antmicro/signal-integrity-test-board/assets/previews/layer1.webp

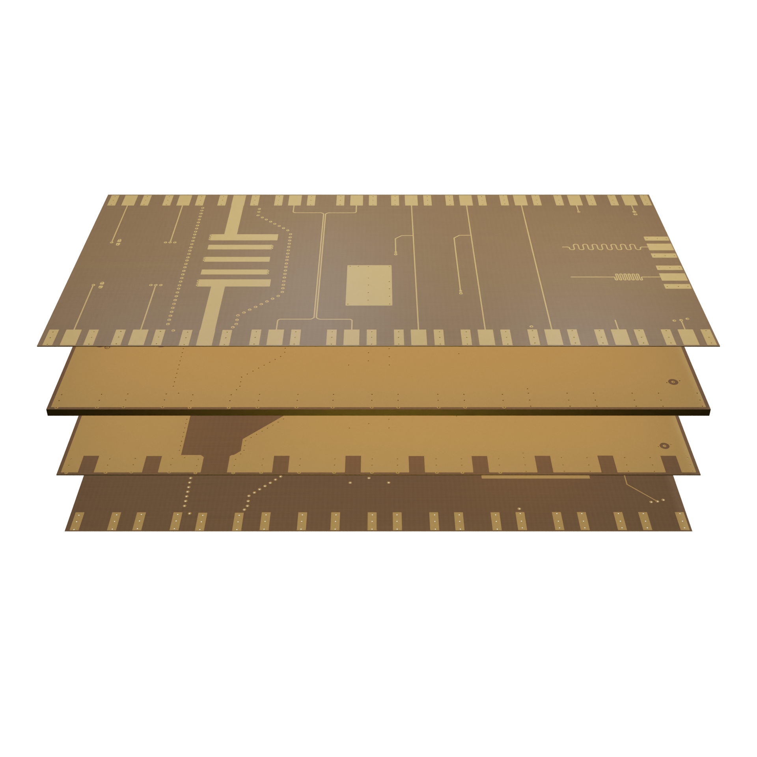
assets/previews/layer1.webp
