antmicro/signal-integrity-test-board/assets/previews/layer3.png

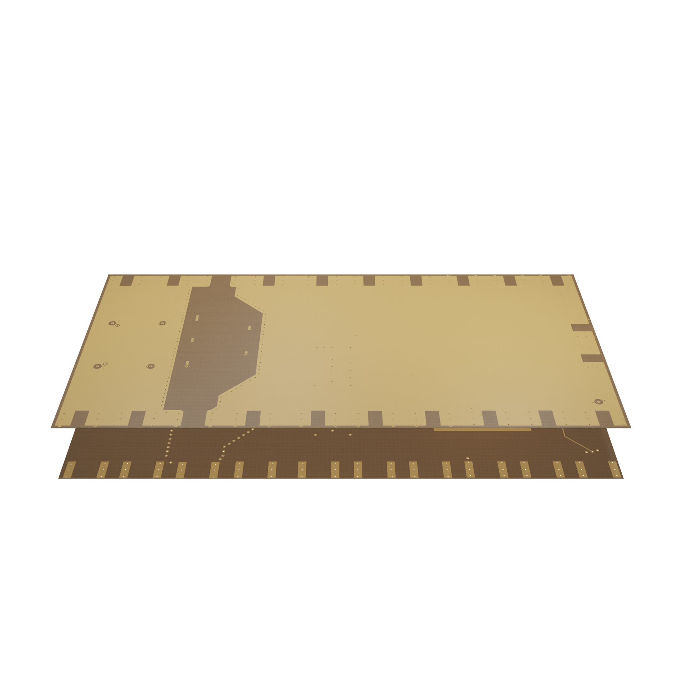
assets/previews/layer3.png
