antmicro/signal-integrity-test-board/assets/previews/layer4.png

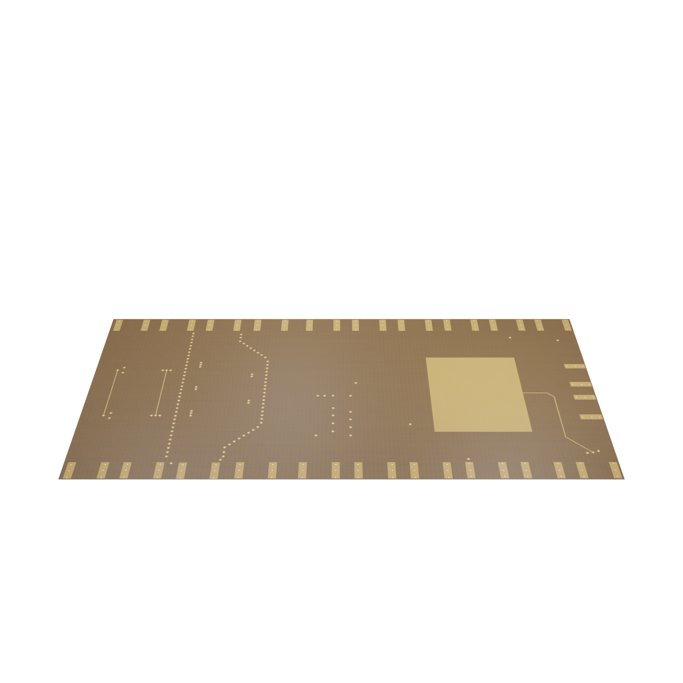
assets/previews/layer4.png
