antmicro/signal-integrity-test-board/assets/previews/leftB.png

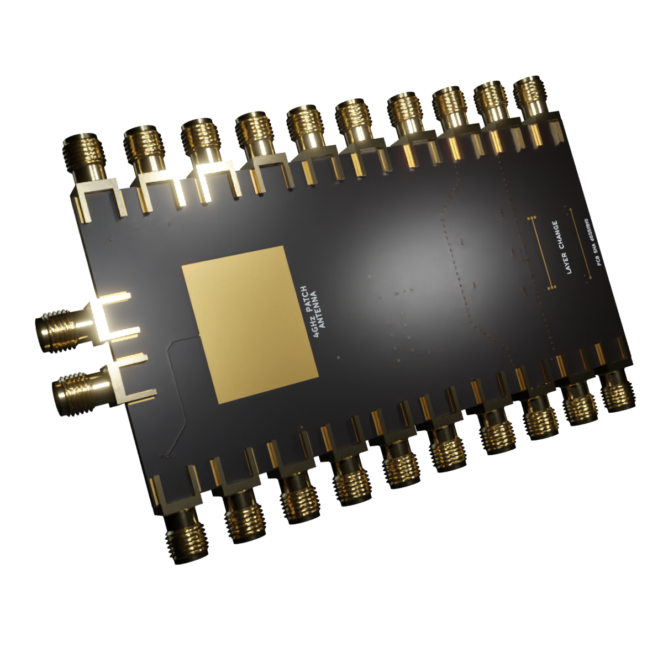
assets/previews/leftB.png
