antmicro/signal-integrity-test-board/assets/previews/leftT.png

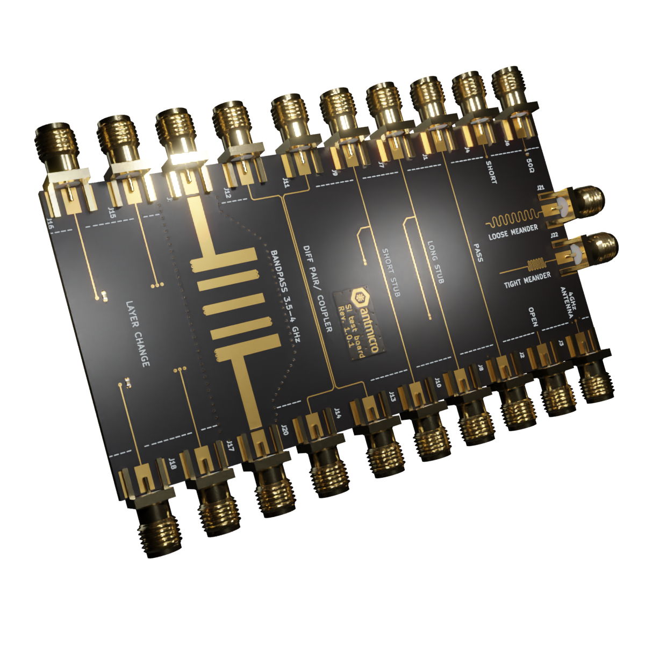
assets/previews/leftT.png
