antmicro/signal-integrity-test-board/assets/previews/orthoB.png

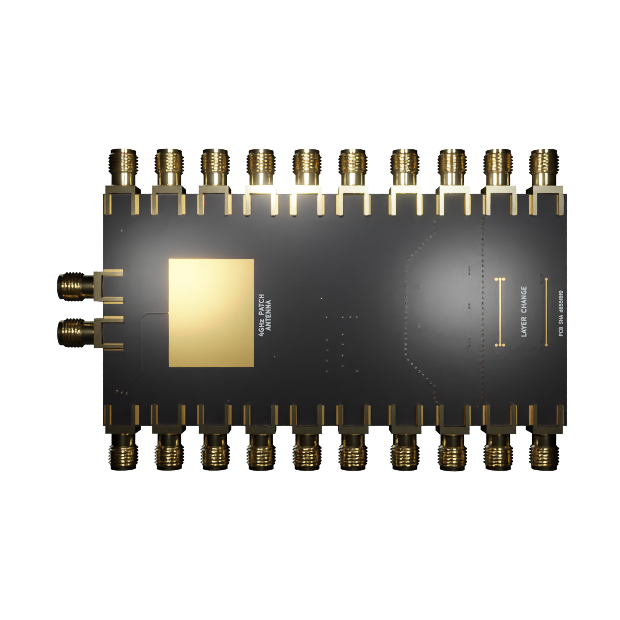
assets/previews/orthoB.png
