antmicro/signal-integrity-test-board/assets/previews/orthoT.png

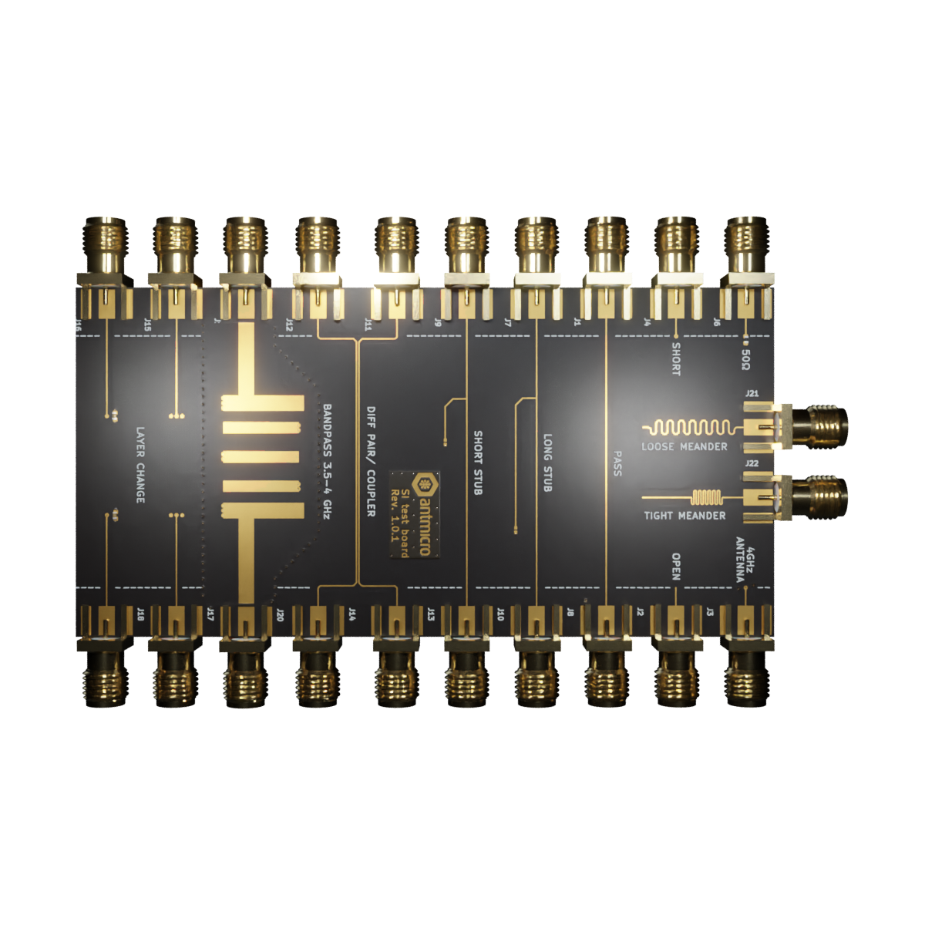
assets/previews/orthoT.png
