antmicro/signal-integrity-test-board/assets/previews/photoB.png

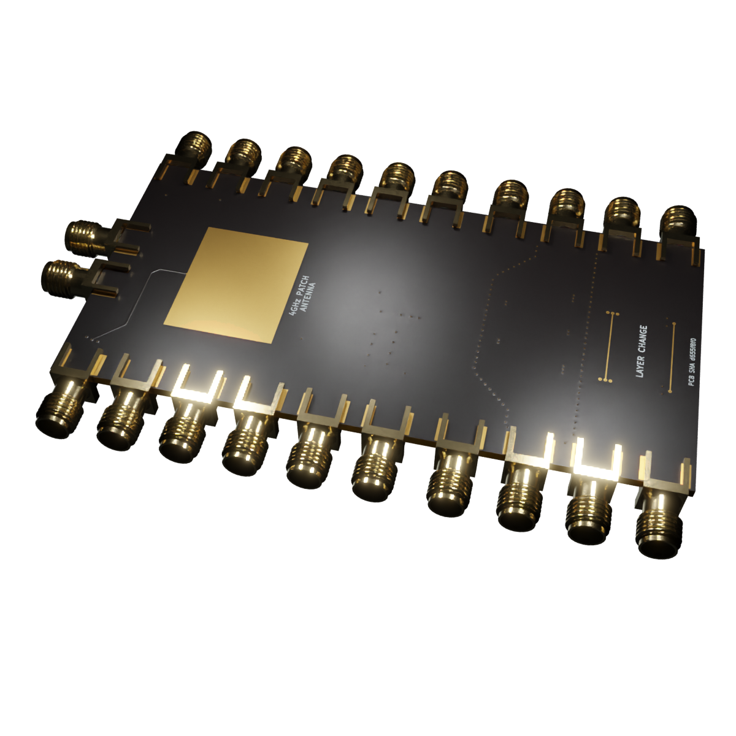
assets/previews/photoB.png
