antmicro/signal-integrity-test-board/assets/previews/photoT.png

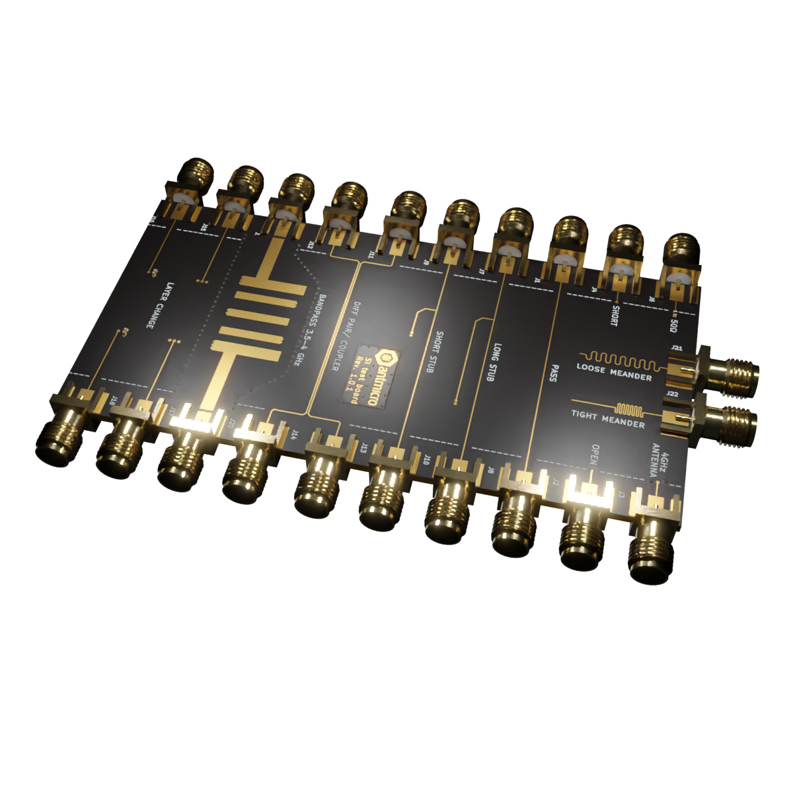
assets/previews/photoT.png
