antmicro/signal-integrity-test-board/assets/previews/rightB.png

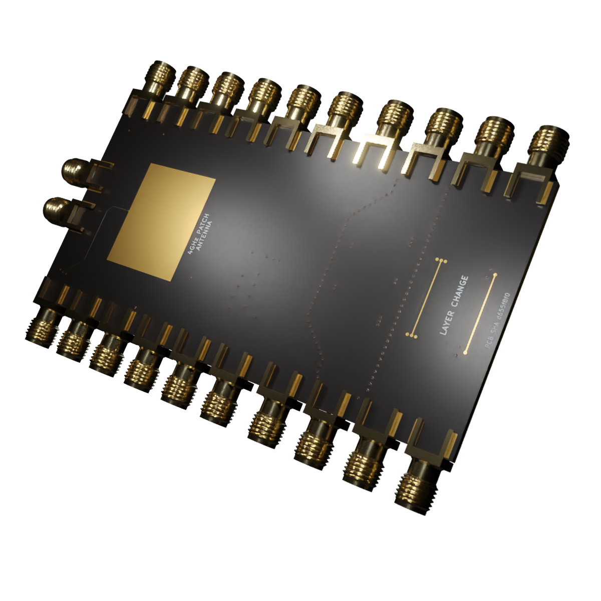
assets/previews/rightB.png
