antmicro/signal-integrity-test-board/assets/previews/rightT.png

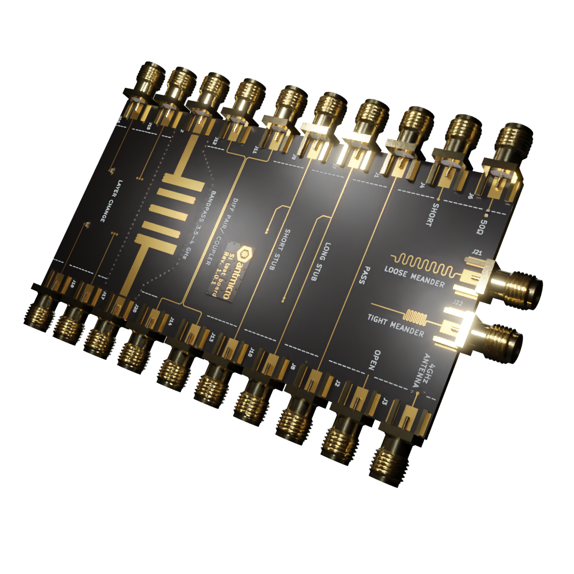
assets/previews/rightT.png
