antmicro/signal-integrity-test-board/assets/si/diff_pair/diff_delay.png

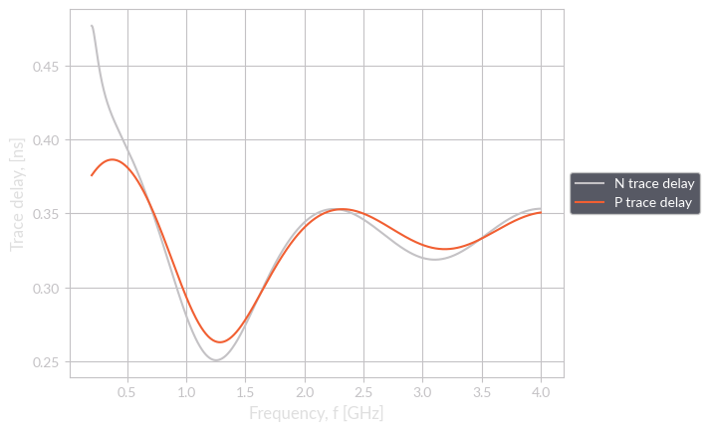
assets/si/diff_pair/diff_delay.png
