antmicro/signal-integrity-test-board/assets/si/diff_pair/S_11_smith.png

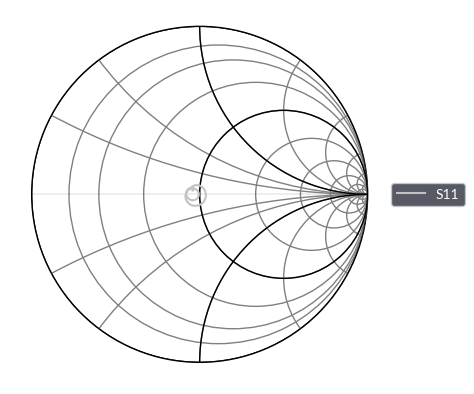
assets/si/diff_pair/S_11_smith.png
