antmicro/signal-integrity-test-board/assets/si/diff_pair/s_param_and_smith_1.png

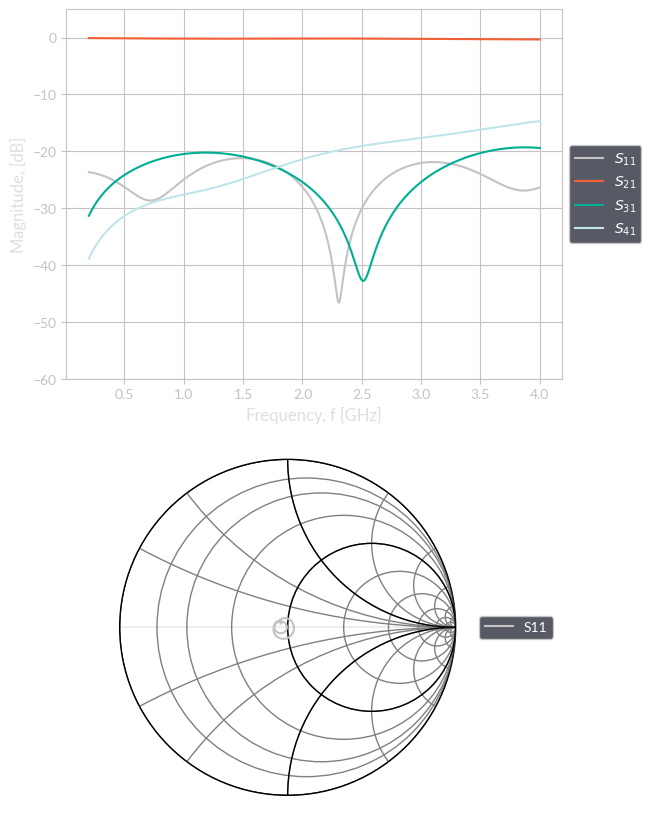
assets/si/diff_pair/s_param_and_smith_1.png
