antmicro/signal-integrity-test-board/assets/si/diff_pair/S_x3.png

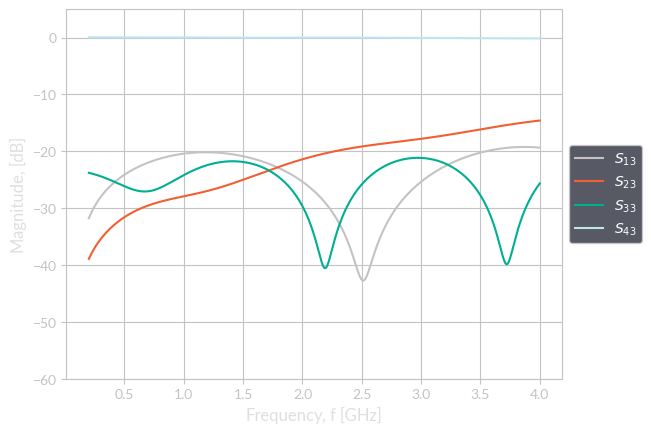
assets/si/diff_pair/S_x3.png
