antmicro/signal-integrity-test-board/assets/si/diff_pair/SDD_Diff.png

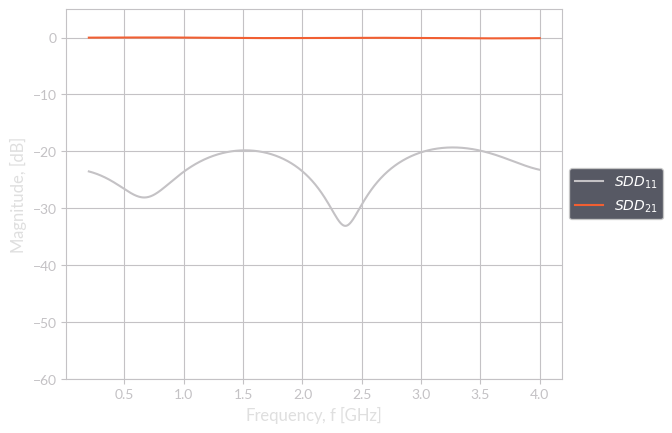
assets/si/diff_pair/SDD_Diff.png
