antmicro/signal-integrity-test-board/assets/si/diff_pair/top_view.png

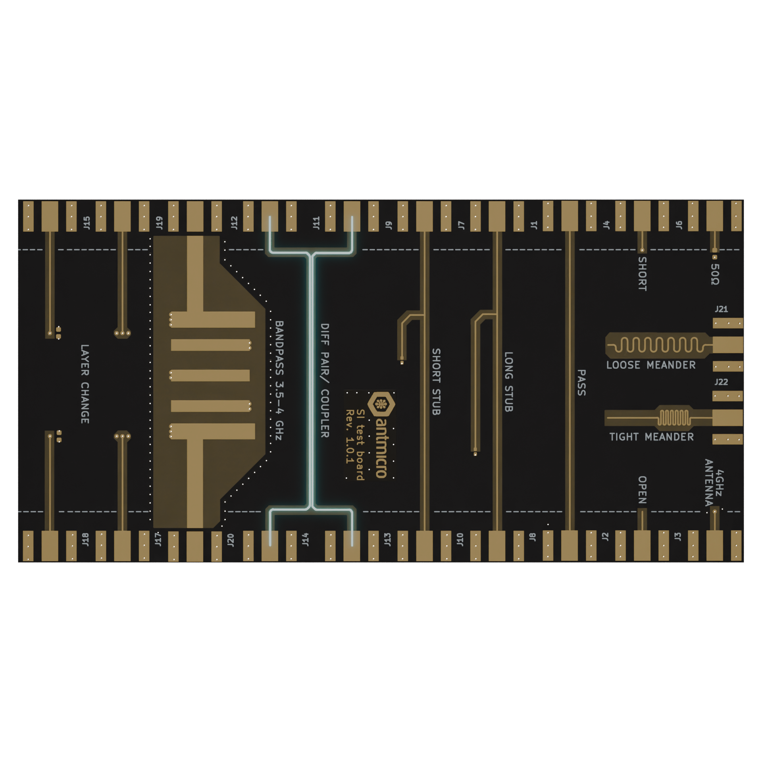
assets/si/diff_pair/top_view.png
