antmicro/signal-integrity-test-board/assets/si/diff_pair/Z_1.png

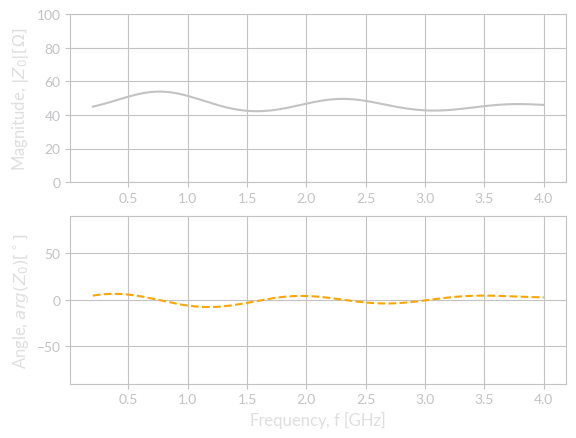
assets/si/diff_pair/Z_1.png
