antmicro/signal-integrity-test-board/assets/si/diff_pair/Z_diff.png

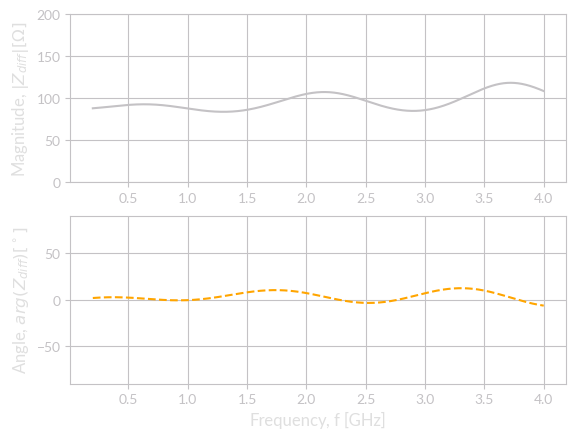
assets/si/diff_pair/Z_diff.png
