antmicro/signal-integrity-test-board/assets/si/layer-change-1/s_param_and_smith_1.png

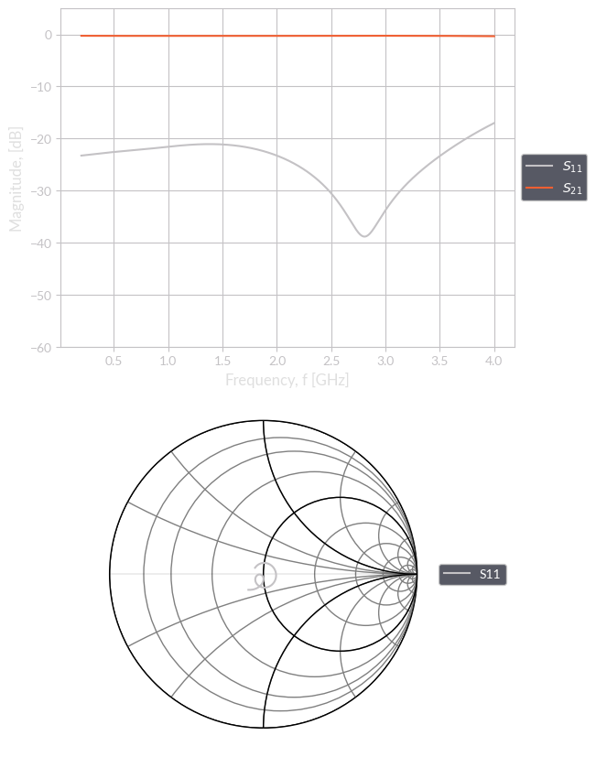
assets/si/layer-change-1/s_param_and_smith_1.png
