antmicro/signal-integrity-test-board/assets/si/layer-change-1/S_x1.png

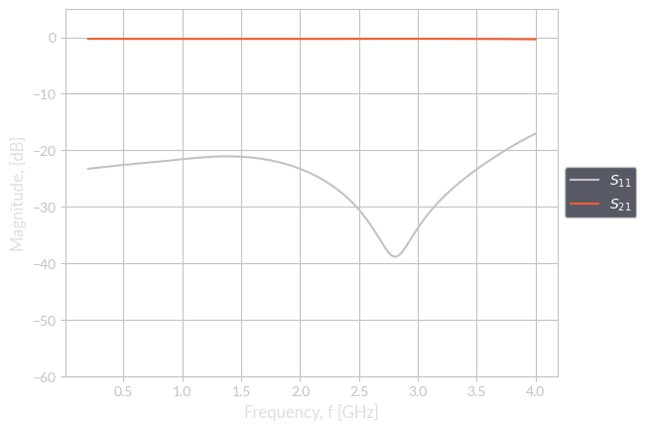
assets/si/layer-change-1/S_x1.png
