antmicro/signal-integrity-test-board/assets/si/layer-change-2/S_x1.png

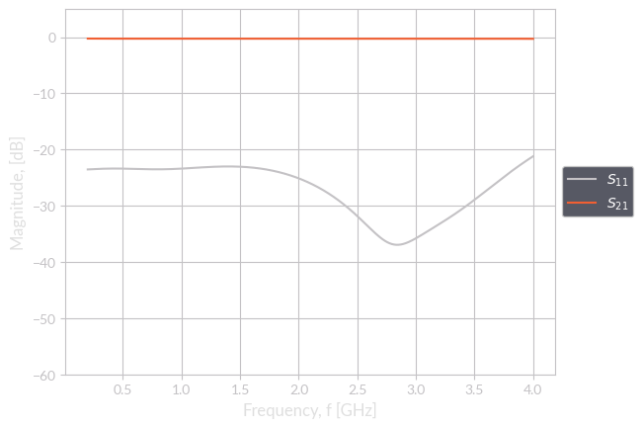
assets/si/layer-change-2/S_x1.png
