antmicro/signal-integrity-test-board/assets/si/long-stub/S_11_smith.png

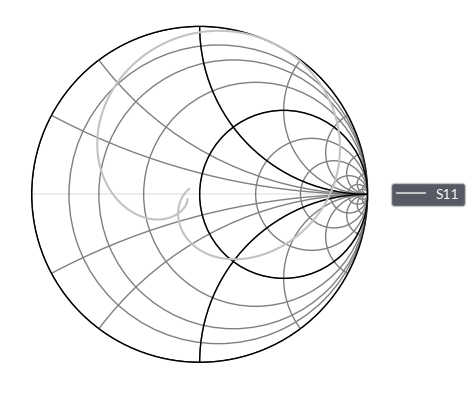
assets/si/long-stub/S_11_smith.png
