antmicro/signal-integrity-test-board/assets/si/long-stub/s_param_and_smith_1.png

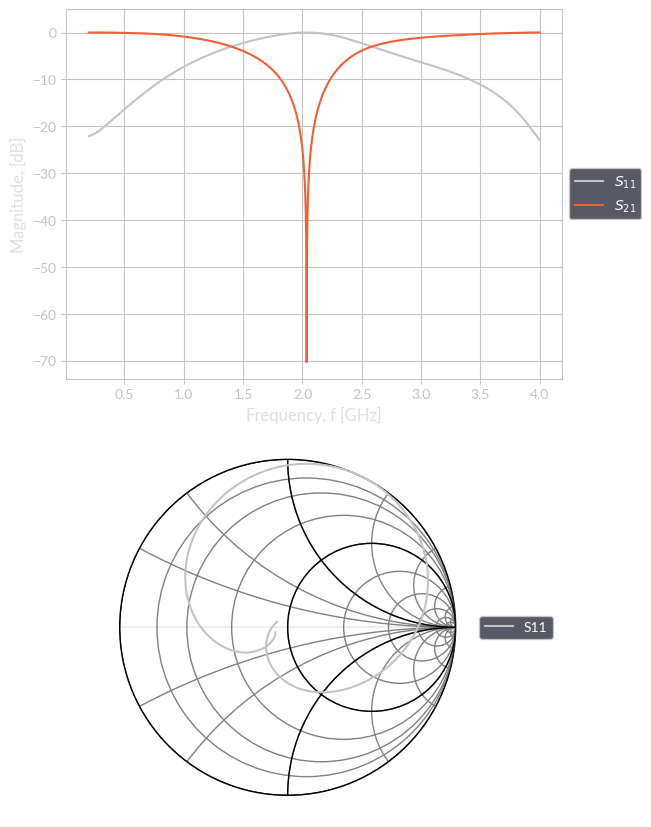
assets/si/long-stub/s_param_and_smith_1.png
