antmicro/signal-integrity-test-board/assets/si/long-stub/S_x1.png

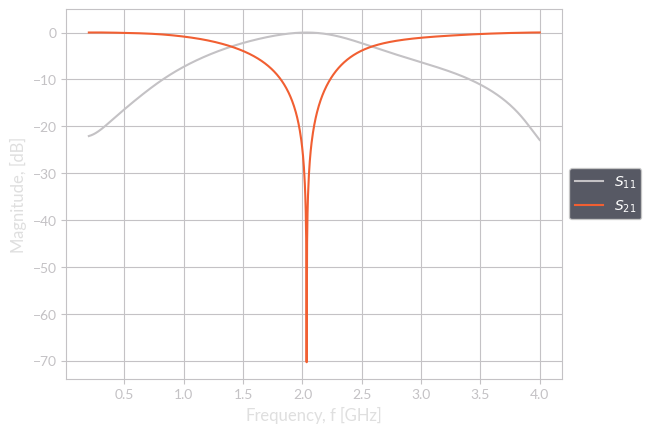
assets/si/long-stub/S_x1.png
