antmicro/signal-integrity-test-board/assets/si/long-stub/Z_1.png

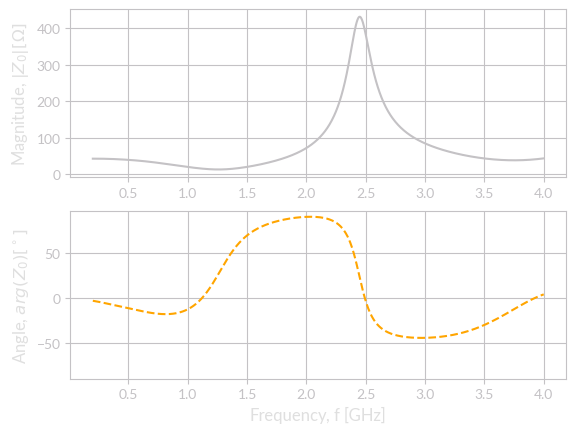
assets/si/long-stub/Z_1.png
