antmicro/signal-integrity-test-board/assets/si/loose-meander/s_param_and_smith_1.png

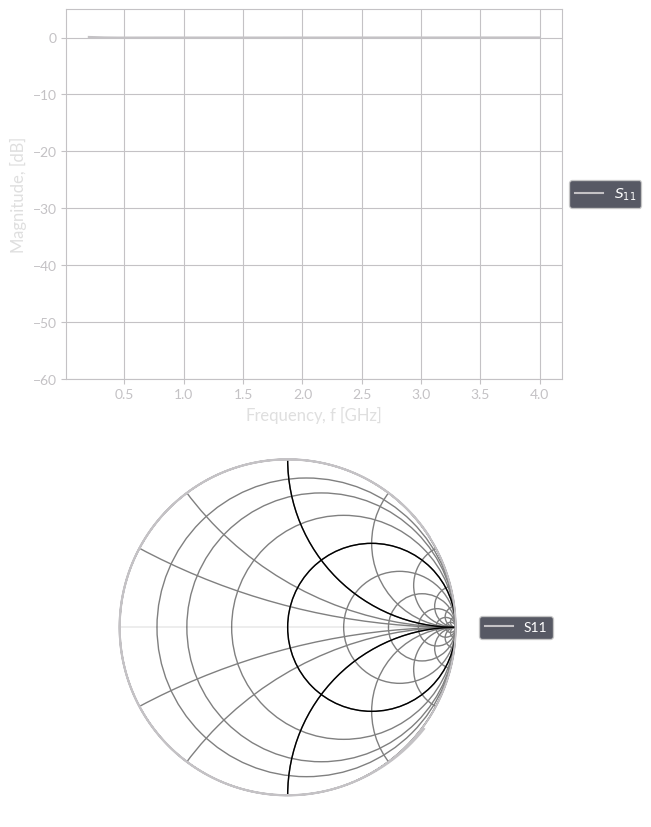
assets/si/loose-meander/s_param_and_smith_1.png
