antmicro/signal-integrity-test-board/assets/si/loose-meander/S_x1.png

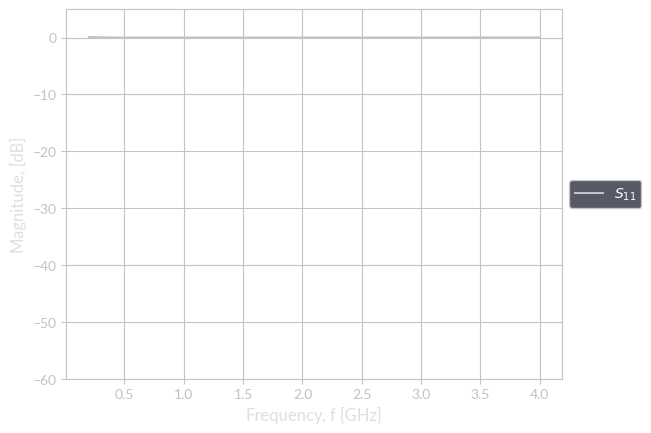
assets/si/loose-meander/S_x1.png
