antmicro/signal-integrity-test-board/assets/si/loose-meander/Z_1.png

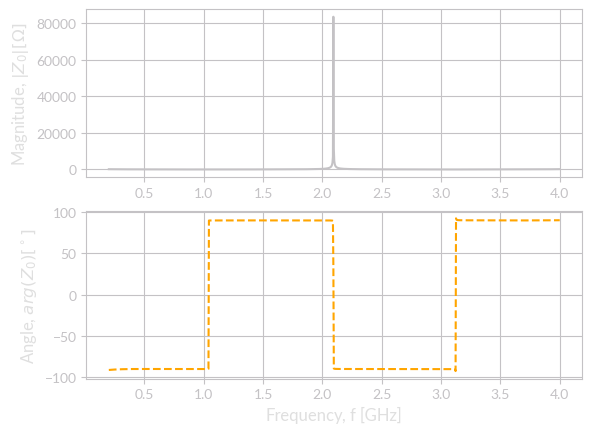
assets/si/loose-meander/Z_1.png
