antmicro/signal-integrity-test-board/assets/si/short-stub/s_param_and_smith_1.png

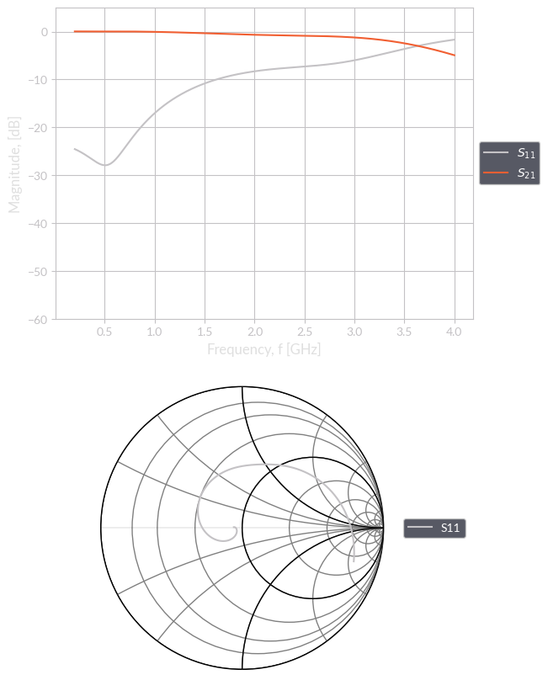
assets/si/short-stub/s_param_and_smith_1.png
