antmicro/signal-integrity-test-board/assets/si/short-stub/Z_1.png

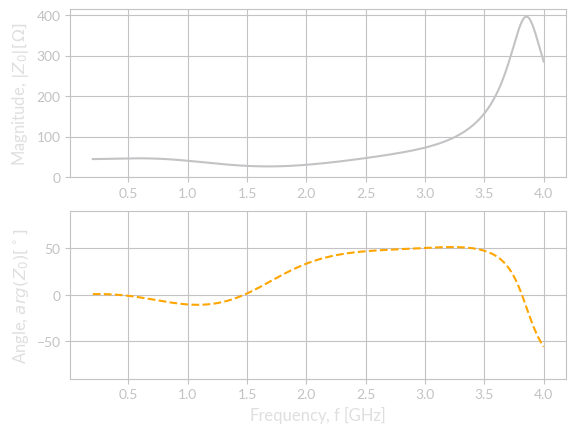
assets/si/short-stub/Z_1.png
