antmicro/signal-integrity-test-board/assets/si/tight-meander/Z_1.png

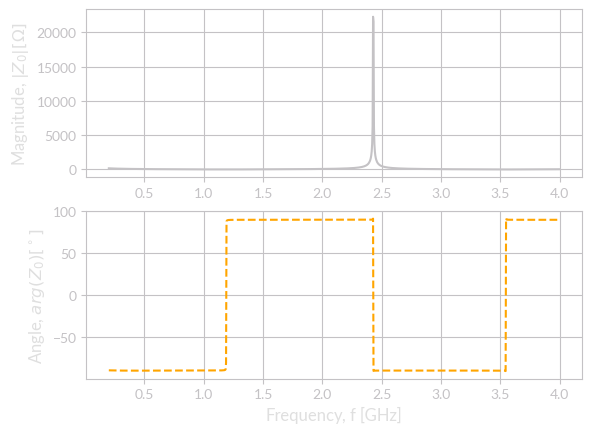
assets/si/tight-meander/Z_1.png
